michelkeijzers/fraxis/Hardware/Grabcad/2004 display/LCD2004 IIC_I2C, 20x4 - Sestava.JPG

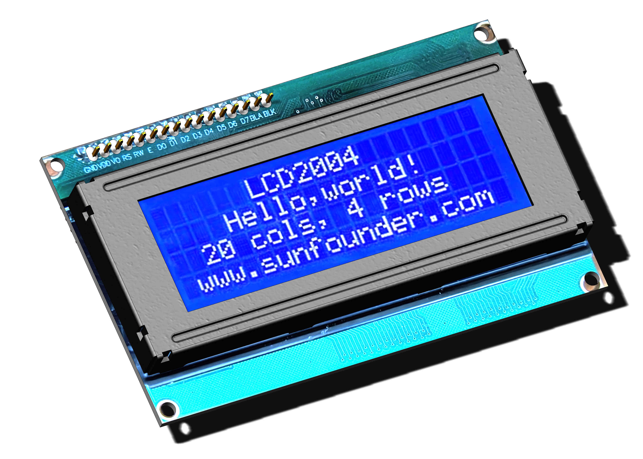
Hardware/Grabcad/2004 display/LCD2004 IIC_I2C, 20x4 - Sestava.JPG
