michelkeijzers/fraxis/Hardware/Grabcad/Mcp23017 module/mcp23017_verso.png

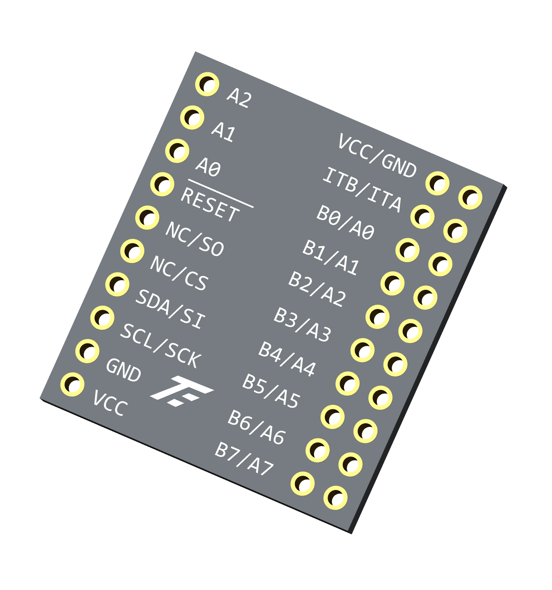
Hardware/Grabcad/Mcp23017 module/mcp23017_verso.png
