michelkeijzers/fraxis/Hardware/Grabcad/Buzzer Module - FC-07/Buzzer Module - FC-07.SLDASM

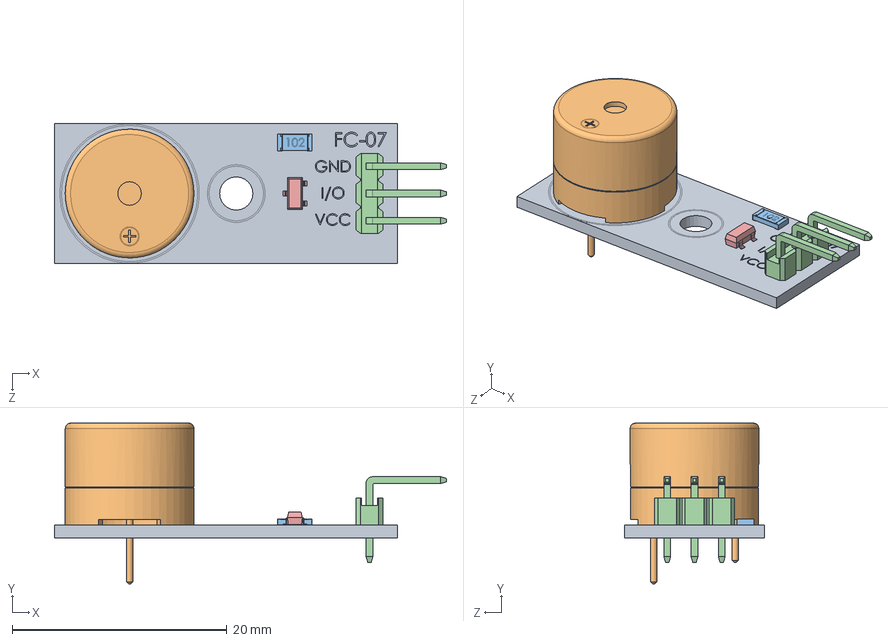
[picture p40: CAD file, 2026-07-04]
Hardware/Grabcad/Buzzer Module - FC-07/Buzzer Module - FC-07.SLDASM
36.5 x 15.0 x 13.1 mm
Buzzer Module - FC-07 - PCB
Buzzer - 7.6mm
Resistor - SMD - 1206
Pin Header - Single Row - Angled - 2.54 - 3x1
Transistör - SMD - BC817 NPN - SOT23
