michelkeijzers/fraxis/Hardware/Grabcad/1506 led lighting profile 1 ledstrip cover/1506_light_profile.stp

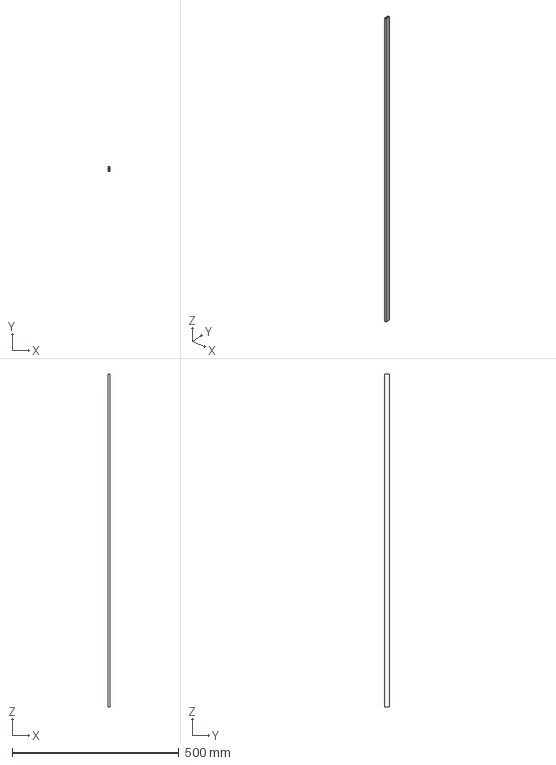
[picture p41: CAD file, 2026-07-04]
Hardware/Grabcad/1506 led lighting profile 1 ledstrip cover/1506_light_profile.stp
6.00 x 15.0 x 1000.0 mm
