michelkeijzers/fraxis/Hardware/Grabcad/BOB-12009/BOB-12009.step

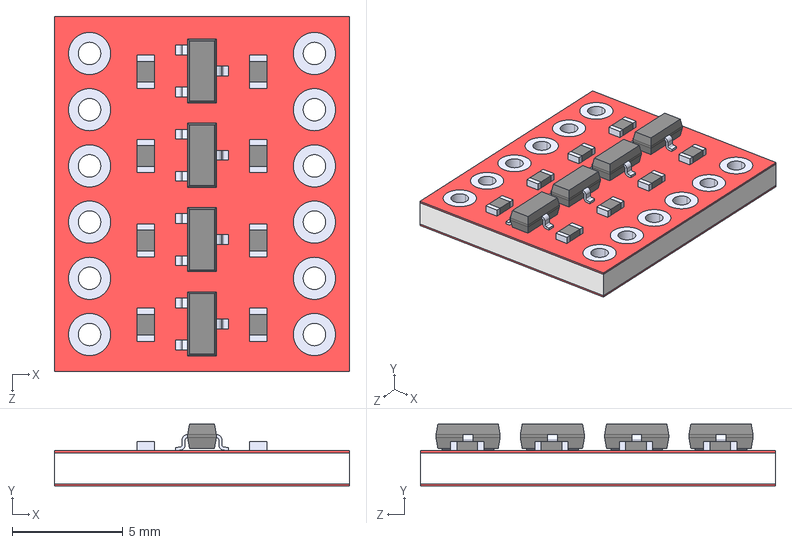
[picture p42: CAD file, 2026-07-23]
Hardware/Grabcad/BOB-12009/BOB-12009.step
13.3 x 2.80 x 16.1 mm
