michelkeijzers/fraxis/main/M10_Composition/Context/DeviceDriversContext.hpp

#pragma once

#include <memory>
#include "../../M30_Messages/Types.hpp"
#include "../../M60_DeviceDrivers/I2c/I2cDeviceDriver.hpp"
#include "../../M60_DeviceDrivers/Spi/SpiDeviceDriver.hpp"
#include "../../M60_DeviceDrivers/Lcd2004/Lcd2004DeviceDriver.hpp"
#include "../../M60_DeviceDrivers/Mcp23017/Mcp23017DeviceDriver.hpp"
#include "../../M60_DeviceDrivers/Tm1637/Tm1637DeviceDriver.hpp"
#include "../../M60_DeviceDrivers/Ws28xx/Ws28xxDeviceDriver.hpp"
#include "../../M60_DeviceDrivers/MicroSdCard/MicroSdCardDeviceDriver.hpp"
#include "../../M60_DeviceDrivers/Audio/AudioDeviceDriver.hpp"
#include "../../M60_DeviceDrivers/Audio/Microphone/Inmp1441DeviceDriver.hpp"
#include "../../M60_DeviceDrivers/Audio/Dac/Max53987aDeviceDriver.hpp"
#include "../../M60_DeviceDrivers/Audio/Buzzer/BuzzerDeviceDriver.hpp"

class DeviceDriversContext
{
public:
    DeviceDriversContext();
    ~DeviceDriversContext();

    void Set(
        std::unique_ptr<I2cDeviceDriver> i2cDeviceDriver,
        std::unique_ptr<SpiDeviceDriver> spiDeviceDriver,
        std::unique_ptr<Lcd2004DeviceDriver> lcd2004DeviceDriver,
        std::unique_ptr<Mcp23017DeviceDriver> mcpDeviceDriver,
        std::unique_ptr<Tm1637DeviceDriver> tm1637DeviceDriverCentralPanel,
        std::unique_ptr<Tm1637DeviceDriver> tm1637DeviceDriverPlayer1,
        std::unique_ptr<Tm1637DeviceDriver> tm1637DeviceDriverPlayer2,
        std::unique_ptr<Ws28xxDeviceDriver> ws28xxDeviceDriver,
        std::unique_ptr<MicroSdCardDeviceDriver> microSdCardDeviceDriver,
        std::unique_ptr<AudioDeviceDriver> audioDeviceDriver,
        std::unique_ptr<Inmp1441DeviceDriver> microphoneDeviceDriver,
        std::unique_ptr<Max53987aDeviceDriver> dacDeviceDriver,
        std::unique_ptr<BuzzerDeviceDriver> buzzerDeviceDriver
    );

    I2cDeviceDriver& GetI2cDeviceDriver();
    SpiDeviceDriver& GetSpiDeviceDriver();
    Lcd2004DeviceDriver& GetLcd2004DeviceDriver();
    Mcp23017DeviceDriver& GetMcp23017DeviceDriver();
    Tm1637DeviceDriver& GetTm1637DeviceDriverCentralPanel();
    Tm1637DeviceDriver& GetTm1637DeviceDriverPlayer1();
    Tm1637DeviceDriver& GetTm1637DeviceDriverPlayer2();
    Tm1637DeviceDriver& GetTm1637DeviceDriverId(
        Types::ETm1637Id tm1637id);
    Ws28xxDeviceDriver& GetWs28xxDeviceDriver();
    MicroSdCardDeviceDriver& GetMicroSdCardDeviceDriver();
    AudioDeviceDriver& GetAudioDeviceDriver();
    Inmp1441DeviceDriver& GetMicrophoneDeviceDriver();
    Max53987aDeviceDriver& GetDacDeviceDriver();
    BuzzerDeviceDriver& GetBuzzerDeviceDriver();

private:
    std::unique_ptr<I2cDeviceDriver> _i2cDeviceDriver;
    std::unique_ptr<SpiDeviceDriver> _spiDeviceDriver;
    std::unique_ptr<Lcd2004DeviceDriver> _lcd2004DeviceDriver;
    std::unique_ptr<Mcp23017DeviceDriver> _mcp23017DeviceDriver;
    std::unique_ptr<Tm1637DeviceDriver> _tm1637DeviceDriverCentralPanel;    
    std::unique_ptr<Tm1637DeviceDriver> _tm1637DeviceDriverPlayer1;
    std::unique_ptr<Tm1637DeviceDriver> _tm1637DeviceDriverPlayer2;
    std::unique_ptr<Ws28xxDeviceDriver> _ws28xxDeviceDriver;
    std::unique_ptr<MicroSdCardDeviceDriver> _microSdCardDeviceDriver;
    std::unique_ptr<AudioDeviceDriver> _audioDeviceDriver;
    std::unique_ptr<Inmp1441DeviceDriver> _microphoneDeviceDriver;
    std::unique_ptr<Max53987aDeviceDriver> _dacDeviceDriver;
    std::unique_ptr<BuzzerDeviceDriver> _buzzerDeviceDriver;
};
