michelkeijzers/fraxis/main/M60_DeviceDrivers/DeviceDriver.cpp

#include "DeviceDriver.hpp"
#include "../M90_Utilities/Assert/Assert.hpp"

DeviceDriver::DeviceDriver()
: _deviceModel(nullptr)
{
}

void DeviceDriver::SetDeviceModel(
    IDeviceModel& deviceModel)
{
    _deviceModel = &deviceModel;
}

IDeviceModel& DeviceDriver::GetDeviceModel() const
{
    return *_deviceModel;
}
