michelkeijzers/fraxis/main/M60_DeviceDrivers/IDeviceDriver.hpp

#pragma once

#include "../M90_Utilities/Initializable/Initializable.hpp"

class IDeviceModel;

class IDeviceDriver : public Initializable
{
public:
    IDeviceDriver();
    virtual ~IDeviceDriver();

    virtual void SetDeviceModel(
        IDeviceModel& deviceModel) = 0;
    virtual IDeviceModel& GetDeviceModel() const = 0;
};
