michelkeijzers/fraxis/main/M60_DeviceDrivers/Ws28xx/Ws28xxDeviceDriver.cpp

#include "Ws28xxDeviceDriver.hpp"
#include "Ws2812Rmt.hpp"
#include "../../M50_DeviceModels/Ws28xx/Ws28xxDeviceModel.hpp"
#include <vector>

#include "../../M90_Utilities/Log/Log.hpp" 
#include "../../M90_Utilities/Time/TimeUtilities.hpp"

Ws28xxDeviceDriver::Ws28xxDeviceDriver()
:   _dataPin(0), 
    _nrOfLeds(0), 
    _rmt(nullptr)
{
}

uint8_t Ws28xxDeviceDriver::GetDataPin() const
{
    return _dataPin;
}

void Ws28xxDeviceDriver::SetDataPin(
    uint8_t dataPin)
{
    _dataPin = dataPin;
}

void Ws28xxDeviceDriver::SetRmt(
    Rmt& rmt)
{
    _rmt = &rmt;
}

void Ws28xxDeviceDriver::Initialize()
{
    _nrOfLeds = GetWs28xxDeviceModel().GetNrOfLeds();
    _ws2812rmt = std::make_unique<Ws2812Rmt>(_dataPin, _nrOfLeds, *_rmt);
    _ws2812rmt->Initialize();
}

Ws28xxDeviceModel& Ws28xxDeviceDriver::GetWs28xxDeviceModel() 
{
    return static_cast<Ws28xxDeviceModel&>(GetDeviceModel()); 
}

void Ws28xxDeviceDriver::WriteToLedStrip()
{
    std::vector<Ws28xxDeviceModel::RgbStruct> destinationBuffer(_nrOfLeds);
    GetWs28xxDeviceModel().FillGrbBufferToSend(destinationBuffer);
    _ws2812rmt->Send(reinterpret_cast<const unsigned char*>( // NOSONAR ESP32 prefers char*
        destinationBuffer.data())); 
}
