michelkeijzers/fraxis/main/Common/Components/LedStrip/LedStripDriver.hpp

#pragma once

#include <cstdint>
#include "../IDriver.hpp"
#include "Ws28xxDeviceModel.hpp"

class LedStripDriver : public IDriver // TODO: Add model and use it
{
public:
    LedStripDriver() = default;
    virtual ~LedStripDriver() = default;

    // Initialize hardware (GPIO, RMT, etc.)
    virtual void Initialize() = 0;

    // Send one physical LED strip buffer
    virtual void Send(const Ws28xxDeviceModel::Pixel* buffer, uint16_t count) = 0;
};
