michelkeijzers/fraxis/main/M10_Composition/Context/DeviceModelsContext.cpp

#include "../../M50_DeviceModels/Lcd2004/Lcd2004DeviceModel.hpp"
#include "../../M50_DeviceModels/Mcp23017/Mcp23017DeviceModel.hpp"
#include "../../M50_DeviceModels/Tm1637/Tm1637DeviceModel.hpp"
#include "../../M50_DeviceModels/Ws28xx/Ws28xxDeviceModel.hpp"
#include "../../M50_DeviceModels/MicroSdCard/MicroSdCardDeviceModel.hpp"
#include "../../M50_DeviceModels/Audio/AudioDeviceModel.hpp"
#include "../../M50_DeviceModels/Audio/Microphone/MicrophoneDeviceModel.hpp"
#include "../../M50_DeviceModels/Audio/Dac/DacDeviceModel.hpp"
#include "../../M50_DeviceModels/Audio/Buzzer/BuzzerDeviceModel.hpp"
#include "DeviceModelsContext.hpp"

DeviceModelsContext::DeviceModelsContext() 
{
}

DeviceModelsContext::~DeviceModelsContext()
{
}

void DeviceModelsContext::Set(
    std::unique_ptr<Lcd2004DeviceModel> lcd2004DeviceModel,
    std::unique_ptr<Mcp23017DeviceModel> mcp23017DeviceModel,
    std::unique_ptr<Tm1637DeviceModel> tm1637DeviceModelCentralPanel,
    std::unique_ptr<Tm1637DeviceModel> tm1637DeviceModelPlayer1,
    std::unique_ptr<Tm1637DeviceModel> tm1637DeviceModelPlayer2,
    std::unique_ptr<Ws28xxDeviceModel> ws28xxDeviceModel,
    std::unique_ptr<MicroSdCardDeviceModel> microSdCardDeviceModel,
    std::unique_ptr<AudioDeviceModel> audioDeviceModel,
    std::unique_ptr<MicrophoneDeviceModel> microphoneDeviceModel,
    std::unique_ptr<DacDeviceModel> dacDeviceModel,
    std::unique_ptr<BuzzerDeviceModel> buzzerDeviceModel)
{
    _lcd2004DeviceModel = std::move(lcd2004DeviceModel);
    _mcp23017DeviceModel = std::move(mcp23017DeviceModel);
    _tm1637DeviceModelCentralPanel = std::move(tm1637DeviceModelCentralPanel);
    _tm1637DeviceModelPlayer1 = std::move(tm1637DeviceModelPlayer1);
    _tm1637DeviceModelPlayer2 = std::move(tm1637DeviceModelPlayer2);
    _ws28xxDeviceModel = std::move(ws28xxDeviceModel);
    _microSdCardDeviceModel = std::move(microSdCardDeviceModel);
    _audioDeviceModel = std::move(audioDeviceModel);
    _microphoneDeviceModel = std::move(microphoneDeviceModel);
    _dacDeviceModel = std::move(dacDeviceModel);
    _buzzerDeviceModel = std::move(buzzerDeviceModel);
}

Lcd2004DeviceModel& DeviceModelsContext::GetLcd2004DeviceModel()              
{
    return *_lcd2004DeviceModel; 
}

Mcp23017DeviceModel&  DeviceModelsContext::GetMcp23017DeviceModel()             
{
    return *_mcp23017DeviceModel; 
}

Tm1637DeviceModel&  DeviceModelsContext::GetTm1637DeviceModelCentralPanel()    
{
    return *_tm1637DeviceModelCentralPanel; 
}

Tm1637DeviceModel&  DeviceModelsContext::GetTm1637DeviceModelPlayer1()          
{
    return *_tm1637DeviceModelPlayer1;
}

Tm1637DeviceModel&  DeviceModelsContext::GetTm1637DeviceModelPlayer2()          
{
    return *_tm1637DeviceModelPlayer2; 
}

Ws28xxDeviceModel&  DeviceModelsContext::GetWs28xxDeviceModel()               
{
    return *_ws28xxDeviceModel; 
}

MicroSdCardDeviceModel&  DeviceModelsContext::GetMicroSdCardDeviceModel()     
{
    return *_microSdCardDeviceModel; 
}

AudioDeviceModel& DeviceModelsContext::GetAudioDeviceModel()
{
    return *_audioDeviceModel;
}

MicrophoneDeviceModel& DeviceModelsContext::GetMicrophoneDeviceModel()
{
    return *_microphoneDeviceModel;
}

DacDeviceModel& DeviceModelsContext::GetDacDeviceModel()
{
    return *_dacDeviceModel;
}

BuzzerDeviceModel& DeviceModelsContext::GetBuzzerDeviceModel()
{
    return *_buzzerDeviceModel;
}
