michelkeijzers/fraxis/main/M10_Composition/Context/TasksContext.cpp

#include "TasksContext.hpp"
#include "../../M00_System/I2cTask.hpp"
#include "../../M00_System/SpiTask.hpp"
#include "../../M00_System/LedStripsTask.hpp"
#include "../../M00_System/DiagnosticsTask.hpp"
#include "../../M00_System/AudioTask.hpp"
#include "../../M20_Applications/ApplicationsTask.hpp"
#include "../../M81_RtosServices/RtosTask/RtosTask.hpp"

TasksContext::TasksContext()
{
}

TasksContext::~TasksContext()
{
}

void TasksContext::Set(
    std::unique_ptr<ApplicationsTask> applicationsTask,
    std::unique_ptr<I2cTask> i2cTask,
    std::unique_ptr<SpiTask> spiTask,
    std::unique_ptr<LedStripsTask> ledStripsTask, 
    std::unique_ptr<DiagnosticsTask> diagnosticsTask,
    std::unique_ptr<AudioTask> audioTask)
{
    _applicationsTask = std::move(applicationsTask);
    _i2cTask = std::move(i2cTask);
    _spiTask = std::move(spiTask);
    _ledStripsTask = std::move(ledStripsTask);
    _diagnosticsTask = std::move(diagnosticsTask);
    _audioTask = std::move(audioTask);
}

ApplicationsTask& TasksContext::GetApplicationsTask() 
{
    return *_applicationsTask; 
}

I2cTask& TasksContext::GetI2cTask() 
{ 
    return *_i2cTask; 
}

SpiTask& TasksContext::GetSpiTask() 
{
    return *_spiTask; 
}

LedStripsTask& TasksContext::GetLedStripsTask() 
{
    return *_ledStripsTask; 
}

DiagnosticsTask& TasksContext::GetDiagnosticsTask() 
{
    return *_diagnosticsTask; 
}

AudioTask& TasksContext::GetAudioTask()
{
    return *_audioTask;
}
