michelkeijzers/fraxis/main/M20_Applications/ApplicationsTask.cpp

#include "../M10_Composition/Context/Context.hpp"
#include "../M10_Composition/Context/DomainModelsContext.hpp"
#include "../M80_Services/Random/Random.hpp"
#include "../M81_RtosServices/RtosQueue/RtosQueue.hpp"
#include "../M90_Utilities/Log/Log.hpp"
#include "../M90_Utilities/Math/MathUtilities.hpp"
#include "ApplicationsTask.hpp"
//#include "../Tasks/Messages/Message.hpp" 
#include <cstring>

ApplicationsTask::ApplicationsTask(
    Context& context) 
:   
    Task(), 
    _context(context), 
    _applicationsManager(_context),
    _i2cInputQueue(_context.GetQueues().GetI2cInputQueue()),
    _i2cInputQueueReader(_i2cInputQueue, _applicationsManager),
    _i2cOutputQueue(_context.GetQueues().GetI2cOutputQueue()),
    _i2cOutputQueueWriter(_i2cOutputQueue, _applicationsManager),
    _spiInputQueue(_context.GetQueues().GetSpiInputQueue()),
    _spiInputQueueReader(_spiInputQueue, _applicationsManager),
    _spiOutputQueue(_context.GetQueues().GetSpiOutputQueue()),
    _spiOutputQueueWriter(_spiOutputQueue, _applicationsManager),
    _ledStripsQueue(_context.GetQueues().GetLedStripsQueue()),
    _ledStripsQueueWriter(_ledStripsQueue, _applicationsManager),
    _queueWriters(_i2cOutputQueueWriter, _spiOutputQueueWriter, _ledStripsQueueWriter),
    _nvsSettings(_context, _applicationsManager, _i2cOutputQueueWriter, _ledStripsQueueWriter)
{
    _applicationsManager.SetQueueWriters(_queueWriters);
}

void ApplicationsTask::Initialize()
{
    _applicationsManager.AddApplications();
}

void ApplicationsTask::Run()
{
    _nvsSettings.ReadNvsSettings();
    
    while (true)
    {
        while (_i2cInputQueueReader.HandleMessage())
        {
            // Handle all messages.
        }

        while (_spiInputQueueReader.HandleMessage())
        {
            // Handle all messages.
        }

        _applicationsManager.Run();
        GetRtosTask().DelayTask(1);
    }
    Log::Exit(Types::ETaskId::ApplicationsTask, "ApplicationsTask::Run");
}

/* static */ void ApplicationsTask::TaskEntry(
    void* param) // NOSONAR: ESP32 expects void*
{
    auto& self = *static_cast<ApplicationsTask*>(param);
    self.Run();
}
