michelkeijzers/fraxis/main/M20_Applications/Applications/Send.cpp

#include "Send.hpp"
#include "../Queues/QueueWriters.hpp"
#include "../Queues/I2cOutputQueueWriter.hpp"
#include "../Queues/LedStripsQueueWriter.hpp"
#include "../../M30_Messages/Types.hpp"
#include "../../M40_DomainModels/I2c/Displays/Lcd2004/Lcd2004.hpp"
#include "../../M90_Utilities/Assert/Assert.hpp"

Send::Send(
    QueueWriters& queueWriters) 
: _queueWriters(queueWriters)
{
}

void Send::Led(
    Types::ELedId ledId, 
    bool state)
{
    _queueWriters.GetI2cOutputQueueWriter().SendLed(ledId, state);
}

void Send::PredefinedCharacter(
    uint8_t slotIndex,
    uint8_t predefinedCharacterIndex)
{
    _queueWriters.GetI2cOutputQueueWriter().SendLcd2004PredefinedCharacter(
        slotIndex, predefinedCharacterIndex);
}

void Send::CustomCharacter(
    uint8_t slotIndex,
    uint8_t data[8])
{
    _queueWriters.GetI2cOutputQueueWriter().SendLcd2004CustomCharacter(slotIndex, data);
}

void Send::Line(
    uint8_t lineNumber, 
    std::string_view line)
{
    Assert::Equals(
        Types::ETaskId::ApplicationsTask, 
        line.length(), 
        Lcd2004::LINE_WIDTH, 
        "Line lengths must be exactly 20 characters");

    _queueWriters.GetI2cOutputQueueWriter().SendLcd2004Line(lineNumber, line);
}

void Send::Tm1637Enable(
    Types::ETm1637Id tm1637Id,
    bool on)
{
    _queueWriters.GetI2cOutputQueueWriter().SendTm1637Enable(tm1637Id, on);
}

void Send::Tm1637Brightness(
    Types::ETm1637Id tm1637Id, 
    uint8_t brightness)
{
    _queueWriters.GetI2cOutputQueueWriter().SendTm1637Brightness(tm1637Id, brightness);
}

void Send::Value(
    Types::ETm1637Id tm1637Id, 
    uint32_t value)
{
    _queueWriters.GetI2cOutputQueueWriter().SendTm1637Value(tm1637Id, value);
}

void Send::Time(
    Types::ETm1637Id tm1637Id, 
    uint8_t first, 
    uint8_t second)
{
    _queueWriters.GetI2cOutputQueueWriter().SendTm1637Time(tm1637Id, first, second);
}

void Send::LedStripsBrightness(
    uint8_t brightness)
{
    _queueWriters.GetLedStripsQueueWriter().SendLedStripsBrightness(brightness);
}

void Send::Pixel(
    uint8_t x, 
    uint8_t y, 
    uint8_t red, 
    uint8_t green, 
    uint8_t blue)
{
    _queueWriters.GetLedStripsQueueWriter().SendPixel(x, y, red, green, blue);
}

void Send::FrameReady()
{
    _queueWriters.GetLedStripsQueueWriter().SendFrameReady();
}
