michelkeijzers/fraxis/main/M20_Applications/Applications/Send.hpp

#pragma once

#include "../../M30_Messages/I2cOutputQueue.hpp"
#include <cstdint>
#include <string>

class QueueWriters;

class Send
{
public:
    explicit Send(
        QueueWriters& queueWriters);
    ~Send() = default;

    /// @defgroup I2C @{
    ///   @defgroup MCP23017 @{
    
    void Led(
        Types::ELedId ledId, bool state);
    
    ///   @} MCP23017

    ///   @defgroup LCD2004 @{
    
    void PredefinedCharacter(
        uint8_t slotIndex,
        uint8_t predefinedCharacterIndex);
    
    void CustomCharacter(
        uint8_t slotIndex,
        uint8_t data[8]);
    
    void Line(
        uint8_t lineNumber, std::string_view line);
    
    ///   @} LCD2004
    /// @} I2C
    
    /// @defgroup TM1637 @{

    void Tm1637Enable(
        Types::ETm1637Id tm1637Id,
        bool on);

    void Tm1637Brightness(
        Types::ETm1637Id tm1637Id,
        uint8_t brightness);
        
    void Value(
        Types::ETm1637Id tm1637Id, 
        uint32_t value);

    void Time(
        Types::ETm1637Id tm1637Id, 
        uint8_t first, 
        uint8_t second);
    
    /// @} TM1637

    /// @defgroup LedStrips @{
    
    void LedStripsBrightness(
    uint8_t brightness);

    void Pixel(
        uint8_t x, 
        uint8_t y, 
        uint8_t red, 
        uint8_t green, 
        uint8_t blue);
    
    void FrameReady();
    
    /// @} LedStrips

    /// @defgroup MicroSdcard @{
    
    // TODOSPI}

    // @} MicroSdCard

private:
    QueueWriters& _queueWriters;
};
