michelkeijzers/fraxis/main/M20_Applications/ApplicationsTask.hpp

#pragma once

#include "ApplicationsManager.hpp"
#include "NvsSettings.hpp"
#include "Queues/I2cInputQueueReader.hpp"
#include "Queues/I2cOutputQueueWriter.hpp"
#include "Queues/SpiInputQueueReader.hpp"
#include "Queues/SpiOutputQueueWriter.hpp"
#include "Queues/LedStripsQueueWriter.hpp"
#include "Queues/QueueWriters.hpp"
#include "../M81_RtosServices/RtosTask/RtosTask.hpp"
#include "../M90_Utilities/Task/Task.hpp"

class Context;
class ApplicationsManager;
class LedStripsQueue;
class I2cInputQueue;
class I2cOutputQueue;
class SpiInputQueue;
class SpiOutputQueue;

class ApplicationsTask : public Task
{
public:
    explicit ApplicationsTask(
        Context& context);
    ~ApplicationsTask() = default;

    void Initialize() override;
    void Run() override;
    static void TaskEntry(
        void* param);

private:
    Context& _context;
    ApplicationsManager _applicationsManager;

    I2cInputQueue& _i2cInputQueue;
    I2cInputQueueReader _i2cInputQueueReader;

    I2cOutputQueue& _i2cOutputQueue;
    I2cOutputQueueWriter _i2cOutputQueueWriter;

    SpiInputQueue& _spiInputQueue;
    SpiInputQueueReader _spiInputQueueReader;

    SpiOutputQueue& _spiOutputQueue;
    SpiOutputQueueWriter _spiOutputQueueWriter;

    LedStripsQueue& _ledStripsQueue;
    LedStripsQueueWriter _ledStripsQueueWriter;

    QueueWriters _queueWriters;

    NvsSettings _nvsSettings;
};
