michelkeijzers/fraxis/main/M50_DeviceModels/Ws28xx/Ws28xxDeviceModel.hpp

#pragma once

#include "../DeviceModel.hpp"
#include "../../M60_DeviceDrivers/Ws28xx/Ws28xxDeviceDriver.hpp"
#include <cstdint>
#include <memory>
#include <vector>
#include <span>

class Ws28xxDeviceModel : public DeviceModel
{
public:
    /// @brief RGB struct, but also used for device driver.
    /// @details DO NOT change the order. Despite the name, the order should be green, red blue. because the struct
    /// is also used inside the device driver to be sent to WS28xx via RMT and the order needs to be specifically 
    /// in grb order.
    struct RgbStruct
    {
        uint8_t green;
        uint8_t red;
        uint8_t blue;
    };

    Ws28xxDeviceModel();
    virtual ~Ws28xxDeviceModel() = default;

    uint16_t GetNrOfLeds() const;
    void SetNrOfLeds(
        uint16_t nrOfLeds);
    void SetMaxCurrentConsumption(
        uint16_t maxCurrentConsumption);
    void Initialize() override;

    void SetBrightness(
        uint8_t brightness);

    void SetPixel(
        uint16_t index,
        uint8_t red,
        uint8_t green,
        uint8_t blue);

    static bool IsRgbEqual(
        RgbStruct a, 
        RgbStruct b);

    virtual void FillGrbBufferToSend(
        std::vector<Ws28xxDeviceModel::RgbStruct>& rgbBuffer);
    void SetFrameReady();

    /// @brief Get leds, only for GDI simulator
    RgbStruct* GetLeds();

private:
    uint8_t _brightness;
    
    // NOSONAR Keep RgbStruct over std::vector due to performance
    std::unique_ptr<RgbStruct[]> _leds; // NOSONAR
    uint16_t _nrOfLeds;
    uint16_t _maxCurrentConsumption;
    bool _frameReady;

    RgbStruct CreateRgb(
        uint8_t red, 
        uint8_t green, 
        uint8_t blue) const;
};
