michelkeijzers/fraxis/main/M20_Applications/Queues/I2cOutputQueueWriter.hpp

#pragma once

#include "../../M30_Messages/QueueProcessor.hpp"
#include "../../M30_Messages/Types.hpp"
#include <cstdint>
#include <string>

class I2cOutputQueue;
class ApplicationsManager;

class I2cOutputQueueWriter : public QueueProcessor
{
public:
    I2cOutputQueueWriter(
        I2cOutputQueue& i2cOutputQueue, 
        ApplicationsManager& applicationsManager);

    ~I2cOutputQueueWriter() = default;
    
    void SendLed(
        Types::ELedId, 
        bool state);

    void SendLcd2004PredefinedCharacter(
        uint8_t slotIndex,
        uint8_t predefinedCharacterIndex);
    
    void SendLcd2004CustomCharacter(
        uint8_t slotIndex,
        uint8_t data[8]);
    
    void SendLcd2004Line(
        uint8_t lineNumber, 
        std::string_view line);

    void SendTm1637Enable(
        Types::ETm1637Id tm1637Id,
        bool on);

    void SendTm1637Brightness(
        Types::ETm1637Id tm1637Id, 
        uint8_t brightness);

    void SendTm1637Value(
        Types::ETm1637Id tm1637Id, 
        uint32_t value);
    
    void SendTm1637Time(
        Types::ETm1637Id tm1637Id,
        uint8_t first,
        uint8_t second);

private:
    I2cOutputQueue& GetI2cOutputQueue();

    ApplicationsManager& _applicationsManager;  
};
