michelkeijzers/fraxis/main/M40_DomainModels/Spi/SpiInputQueueWriter.cpp

#include "SpiInputQueueWriter.hpp"
#include "MicroSdCard/MicroSdCard.hpp"
#include "../../M30_Messages/SpiInputQueue.hpp"   
#include "../../M90_Utilities/Log/Log.hpp" 

SpiInputQueueWriter::SpiInputQueueWriter(
    SpiInputQueue& spiInputQueue, 
    MicroSdCard& microSdCard)
:  
    _microSdCard(microSdCard)
{
    SetQueue(spiInputQueue);
}

SpiInputQueueWriter::~SpiInputQueueWriter()
{
}

SpiInputQueue& SpiInputQueueWriter::GetSpiInputQueue()
{
    return static_cast<SpiInputQueue&>(GetQueue());
}

void SpiInputQueueWriter::SendWrite()
{
//     if (joystick.GetButtonStateDirty().IsDirty())
//     {
//         I2cInputQueue::Message message;
//         message.type = I2cInputQueue::Message::EType::JoystickButton;
//         message.joystickButton.id = joystick.GetId();
//         message.joystickButton.pressed = joystick.GetButtonState();
//         GetI2cInputQueue().GetRtosQueue().Send(&message, 0);
//         Log::Text(Types::ETaskId::I2cTask, "JS Button sent");
//         joystick.GetButtonStateDirty().ClearDirty();
//     }

    if (_microSdCard.GetDirty().IsDirty())
    {
        //TODOSPI
        SpiInputQueue::Message message;
        message.type = SpiInputQueue::Message::EType::TODO;
        GetSpiInputQueue().GetRtosQueue().Send(&message, 0);
        Log::Text(Types::ETaskId::SpiTask, "SPI messages sent");
        _microSdCard.GetDirty().ClearDirty();
    }
}
