michelkeijzers/fraxis/main/M00_System/DiagnosticsManager.cpp

#include "DiagnosticsManager.hpp"
#include "../M10_Composition/Context/Context.hpp"
#include "../M10_Composition/Context/ServicesContext.hpp"
#include "../M80_Services/Uart/Uart.hpp"
#include "../M90_Utilities/Assert/Assert.hpp"
#include "../M90_Utilities/String/StringUtilities.hpp"
#include <string.h>

DiagnosticsManager::DiagnosticsManager(Context& context)
:   _context(context)
{
}

void DiagnosticsManager::OnTaskData(
    Types::ETaskId taskId, 
    uint64_t timeStamp, 
    uint64_t stackSize)
{
    TaskDataStruct taskData
    {
        static_cast<uint8_t>(taskId),
        timeStamp,
        stackSize
    };

    _context.GetServices().GetUart().Send((const char*)&taskData, sizeof(taskData));
}

void DiagnosticsManager::OnLogEntry(
    Types::ETaskId taskId, 
    uint64_t timeStamp, 
    Types::ELogLevel logLevel,
    const char* text)
{
    Assert::IsNotNullptr(taskId, (void*) text, "text");

    LogEntryStruct logEntry
    {
        static_cast<uint8_t>(taskId),
        timeStamp,
        static_cast<uint8_t>(logLevel),
        {}
    };
    StringUtilities::CopyToBuffer(text, logEntry.text, DiagnosticsQueue::MAX_LOG_ENTRY_TEXT_LENGTH);
    _context.GetServices().GetUart().Send((const char*)&logEntry, sizeof(logEntry));
}
