michelkeijzers/fraxis/main/M20_Applications/Queues/I2cInputQueueReader.hpp

#pragma once

#include "../../M30_Messages/QueueProcessor.hpp"

class I2cInputQueue;
class ApplicationsManager;

class I2cInputQueueReader : public QueueProcessor
{
public:
    I2cInputQueueReader(
        I2cInputQueue& i2CinputQueue, 
        ApplicationsManager& applicationsManager);
    ~I2cInputQueueReader() = default;
    
    bool HandleMessage();

private:
    I2cInputQueue& GetI2cInputQueue();
    
    ApplicationsManager& _applicationsManager;
};
