michelkeijzers/fraxis/main/M10_Composition/Builder/EspBuilder.hpp

#ifdef ESP_PLATFORM

#pragma once

#include "Builder.hpp"

// Forward declarations of Context
class Context;

class EspBuilder : public Builder
{
public:
    EspBuilder(
        Context& context);
    ~EspBuilder();

protected:
    void BuildServicesContext() override;
};

#endif // ESP_PLATFORM
